zamojski/PirBOX-LITE/img/DSC00860.JPG

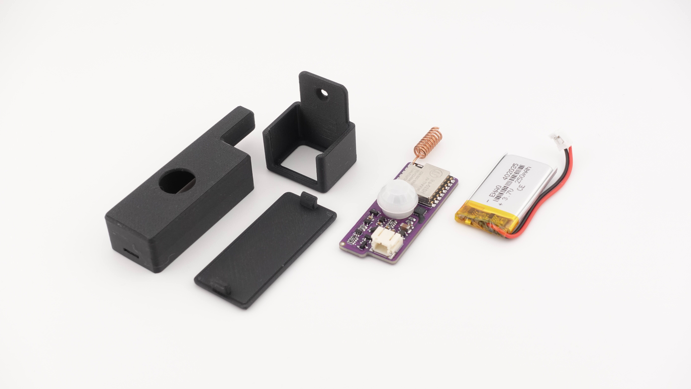
img/DSC00860.JPG
