zamojski/PirBOX-LITE/img/DSC00868.JPG

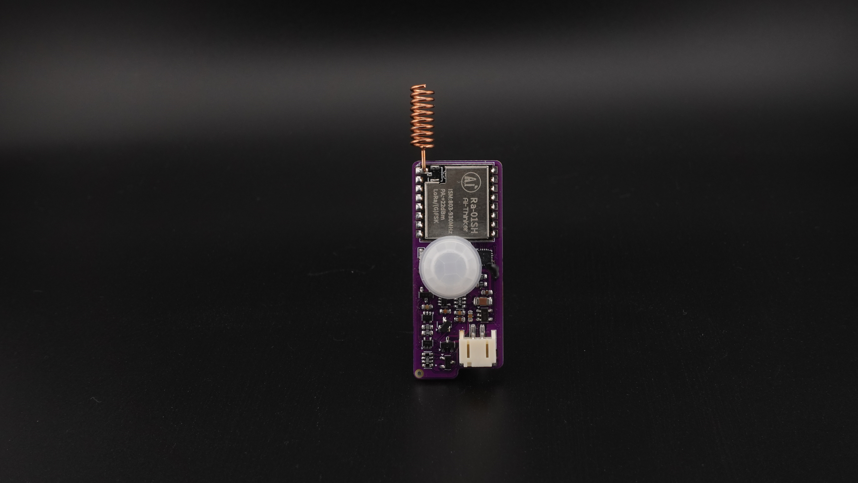
img/DSC00868.JPG
